alan0x/smart-study-lamp/stl/07_corner_cover.stl

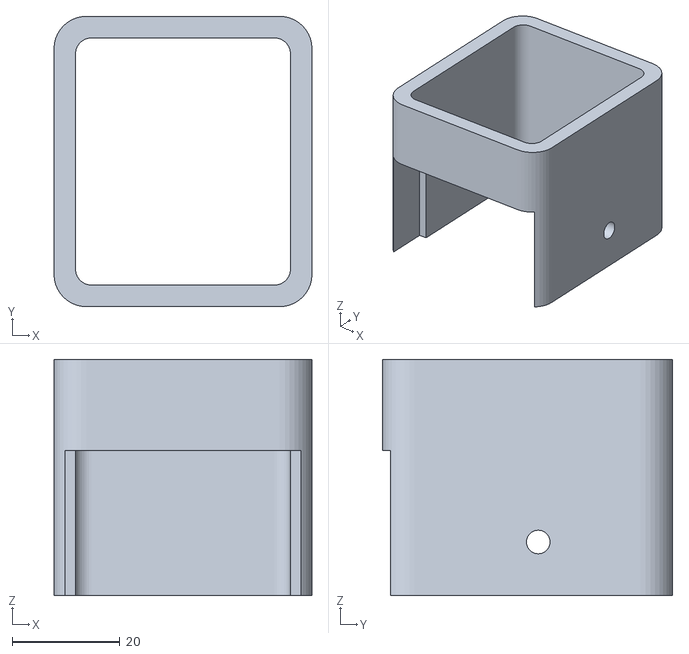
[picture p18: CAD file, 2026-09-15]
stl/07_corner_cover.stl
48.0 x 54.0 x 44.0
