alan0x/smart-study-lamp/stl/03_column_lower_240.stl

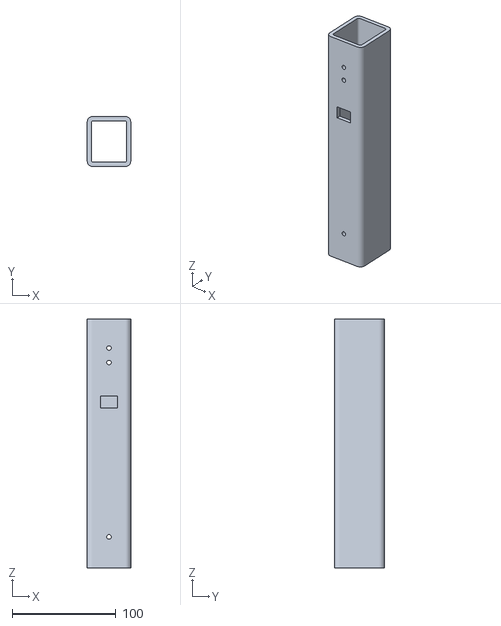
[picture p19: CAD file, 2026-09-15]
stl/03_column_lower_240.stl
42.0 x 48.0 x 240.0
