alan0x/smart-study-lamp/stl/16_tube_fit_coupon.stl

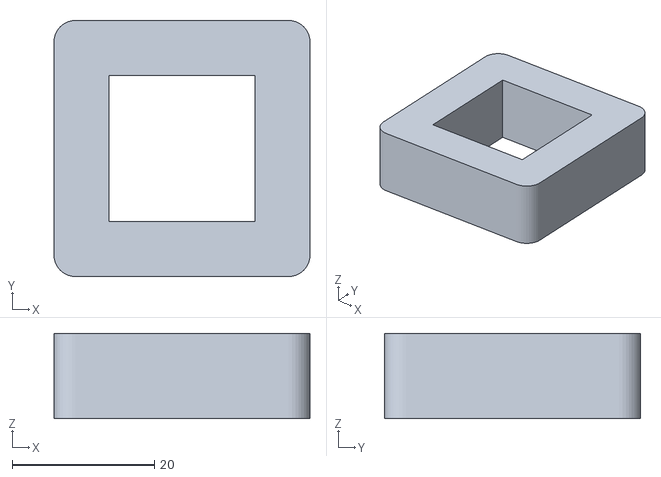
[picture p20: CAD file, 2026-09-15]
stl/16_tube_fit_coupon.stl
36.0 x 36.0 x 12.0
