alan0x/smart-study-lamp/stl/09_UGREEN_59x35x23_cradle.stl

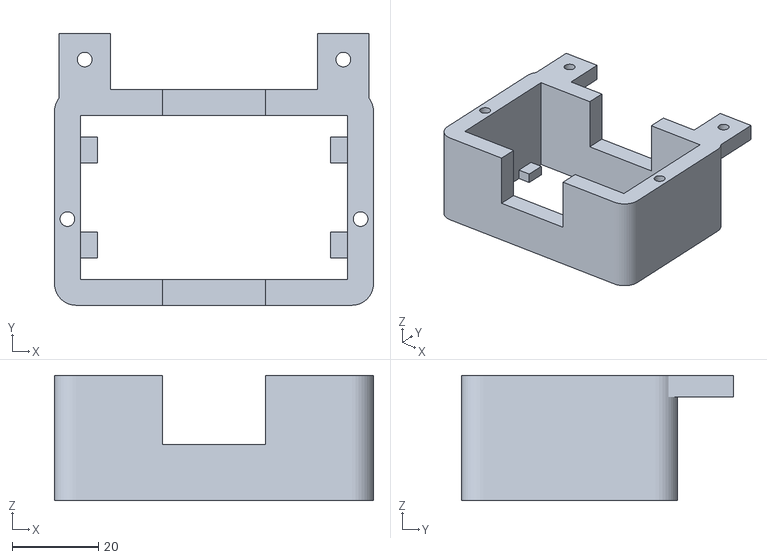
[picture p21: CAD file, 2026-09-15]
stl/09_UGREEN_59x35x23_cradle.stl
74.0 x 63.0 x 29.0
